PSUThings/PSU/Saturn/DesignFiles/180109105549136.png

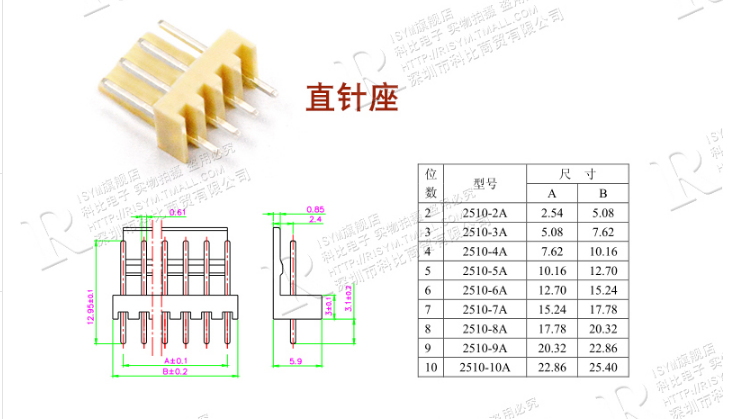
Saturn/DesignFiles/180109105549136.png
