PSUThings/PSU/Dreamcast/DesignFiles/DreamPSU_Test.png

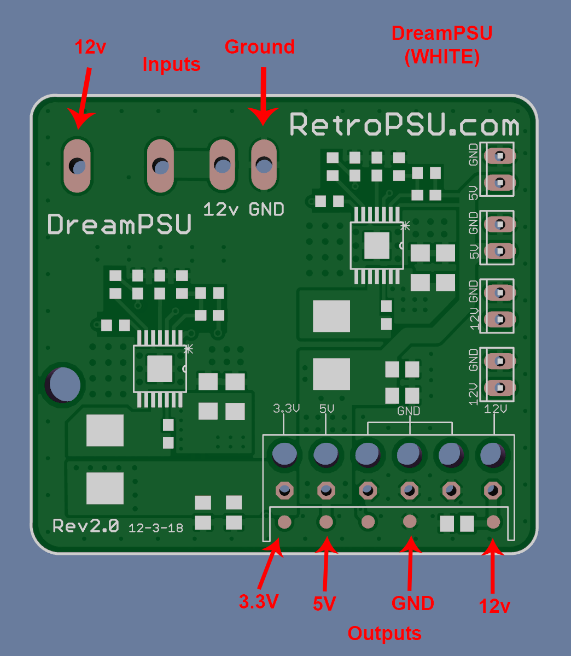
Dreamcast/DesignFiles/DreamPSU_Test.png
